MarkBryanMilligan/LanternPowerMonitor/case/Z2/LPM_Case_Z2_Base.stl

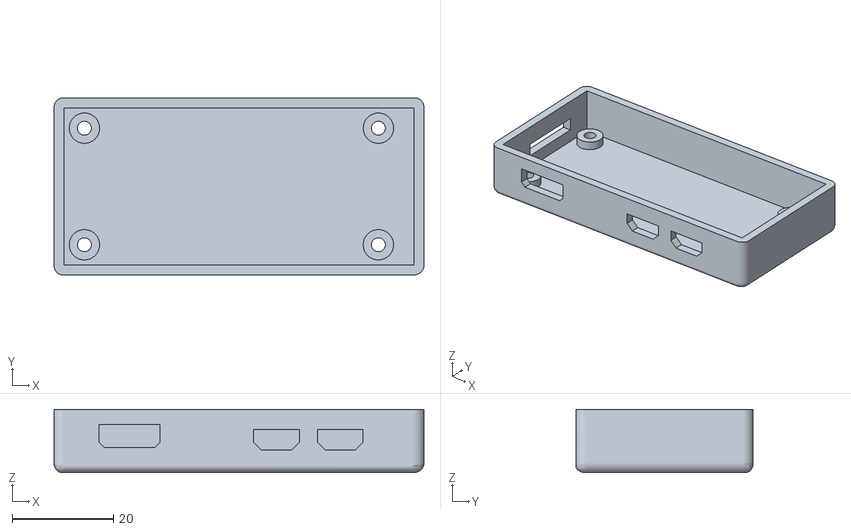
[picture p17: CAD file, 2021-12-04]
case/Z2/LPM_Case_Z2_Base.stl
73.0 x 35.0 x 12.5
