MarkBryanMilligan/LanternPowerMonitor/case/Z2/Z2_GPIO_Lid.stl

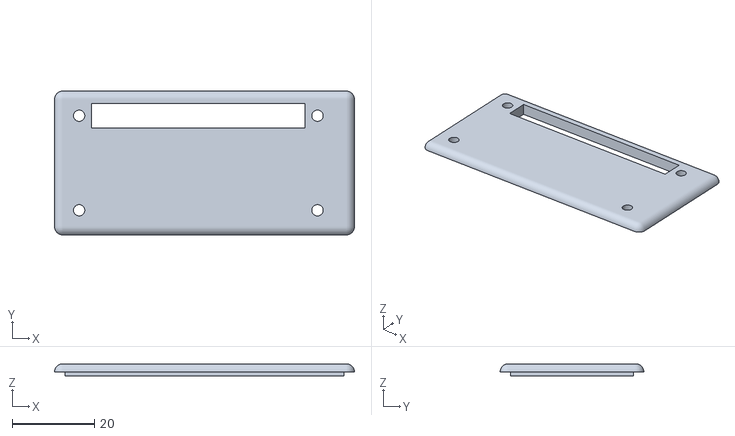
[picture p18: CAD file, 2021-12-04]
case/Z2/Z2_GPIO_Lid.stl
73.0 x 35.0 x 3.00
